ak-c05/100W-IoT-PowerHub/Hardware/Project_Libs/DigitalHUB_3D_Models/TPS259827ONRGET.step

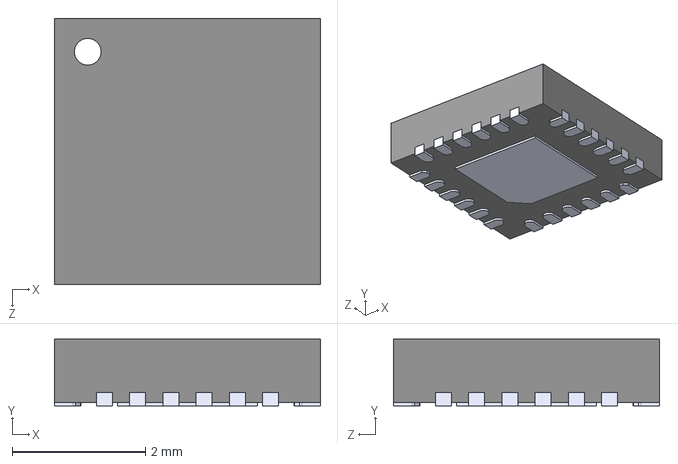
[picture p20: CAD file, 2026-08-28]
Hardware/Project_Libs/DigitalHUB_3D_Models/TPS259827ONRGET.step
4.00 x 1.00 x 4.00 mm
