ak-c05/100W-IoT-PowerHub/Hardware/Project_Libs/DigitalHUB_3D_Models/614004190021.stp

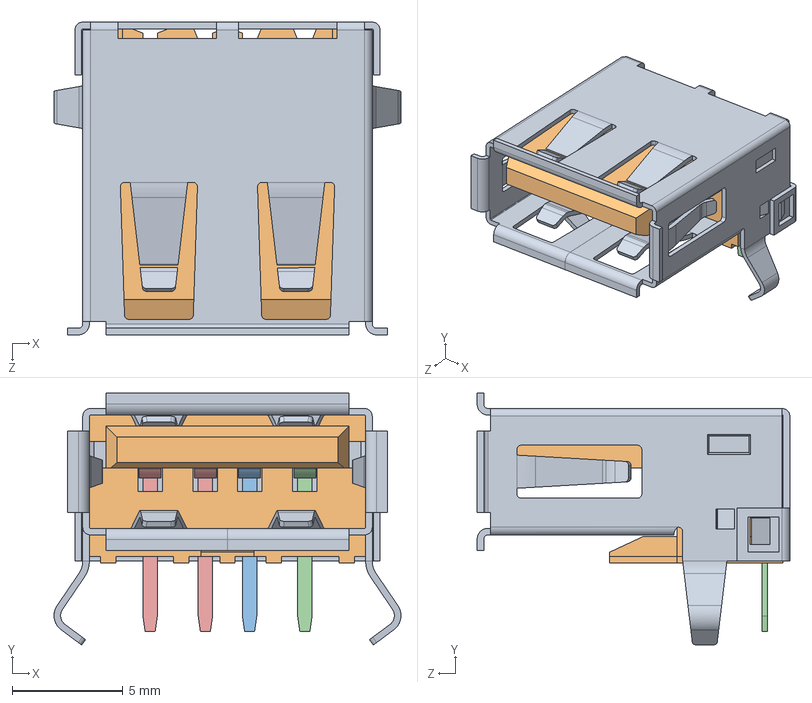
[picture p21: CAD file, 2026-08-28]
Hardware/Project_Libs/DigitalHUB_3D_Models/614004190021.stp
15.7 x 11.4 x 14.1 mm
Cover
Internal Part
Pin
