ak-c05/100W-IoT-PowerHub/Hardware/Project_Libs/DigitalHUB_3D_Models/TPS54302DDCR.step

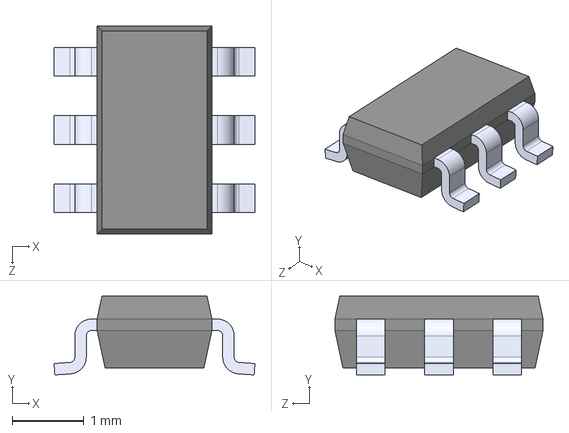
[picture p22: CAD file, 2026-08-28]
Hardware/Project_Libs/DigitalHUB_3D_Models/TPS54302DDCR.step
2.80 x 1.10 x 2.90 mm
